anywhy-io/flake/docs/img/usb.webp

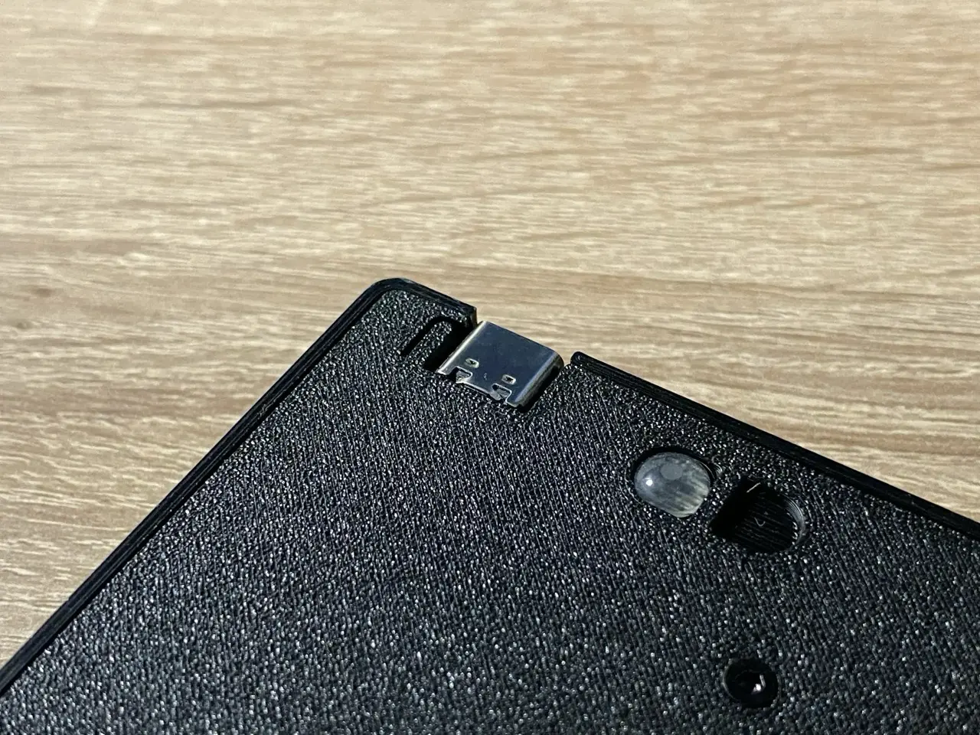
docs/img/usb.webp
