anywhy-io/flake/enclosure/S/without-chamfer/Flake-S-MX-Plate-Right-No-Chamfer.step

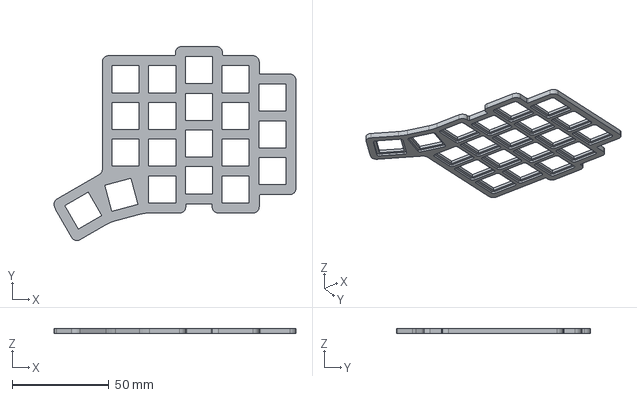
[picture p31: CAD file, 2025-09-25]
enclosure/S/without-chamfer/Flake-S-MX-Plate-Right-No-Chamfer.step
125.2 x 100.4 x 2.80 mm
