anywhy-io/flake/enclosure/L/Flake-L-Top-Right.step

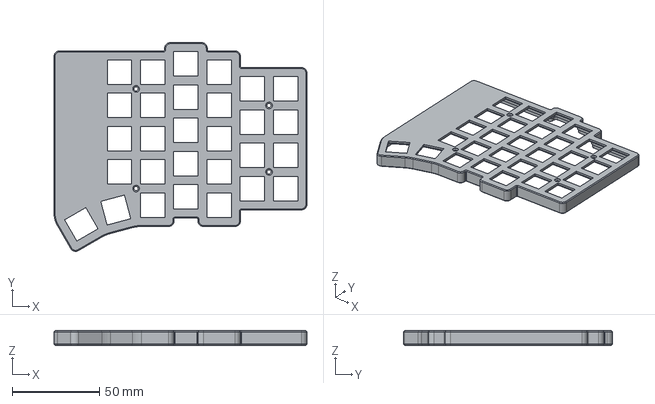
[picture p32: CAD file, 2025-09-20]
enclosure/L/Flake-L-Top-Right.step
144.6 x 119.4 x 8.30 mm
